garnetgrimm/Picochord/pcb/image/keypad.png

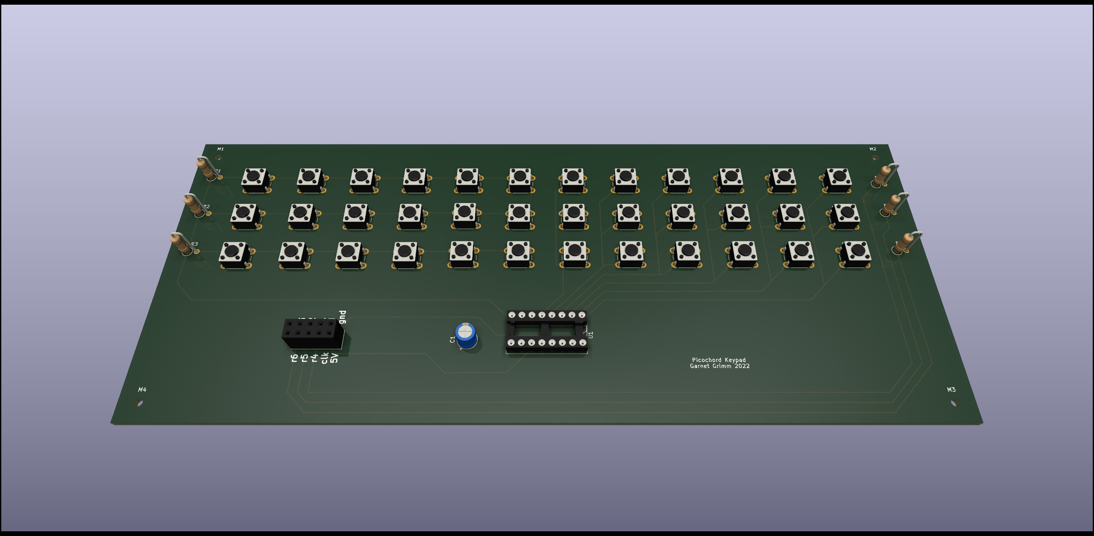
pcb/image/keypad.png
