garnetgrimm/Picochord/pcb/image/speaker_pcb.png

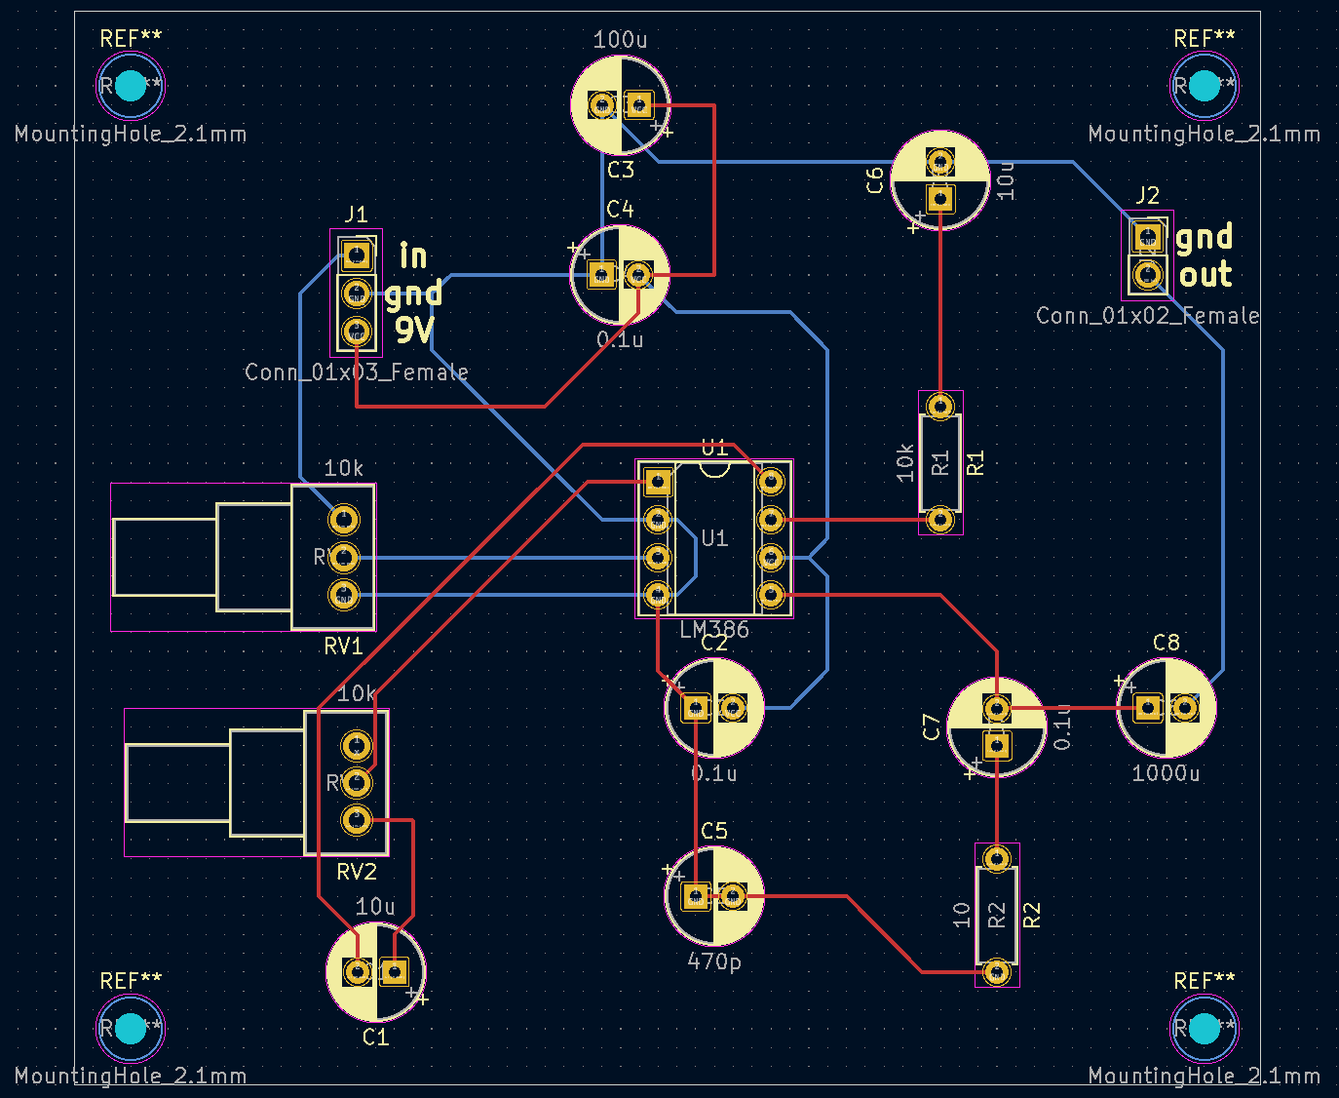
pcb/image/speaker_pcb.png
